rchampeimont/arduino_remote_drawing/3D_model/back.jpg

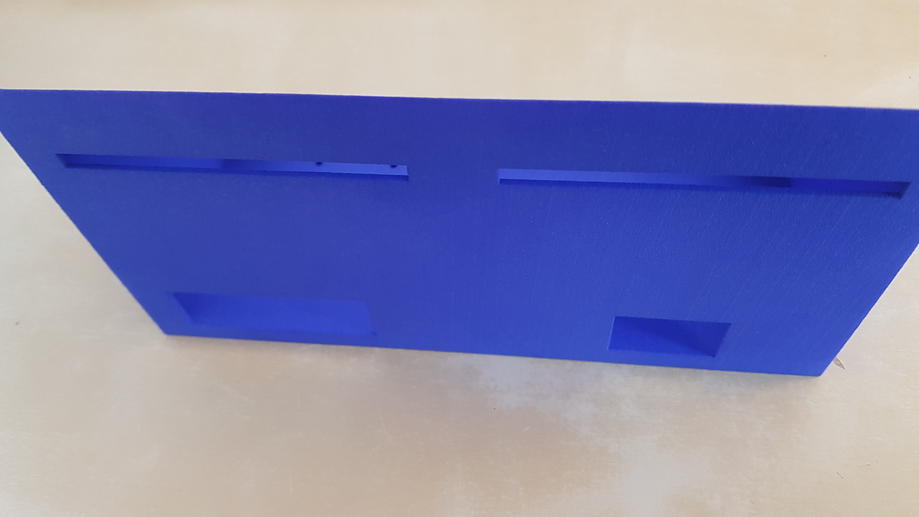
3D_model/back.jpg
