rchampeimont/arduino_remote_drawing/3D_model/bottom.jpg

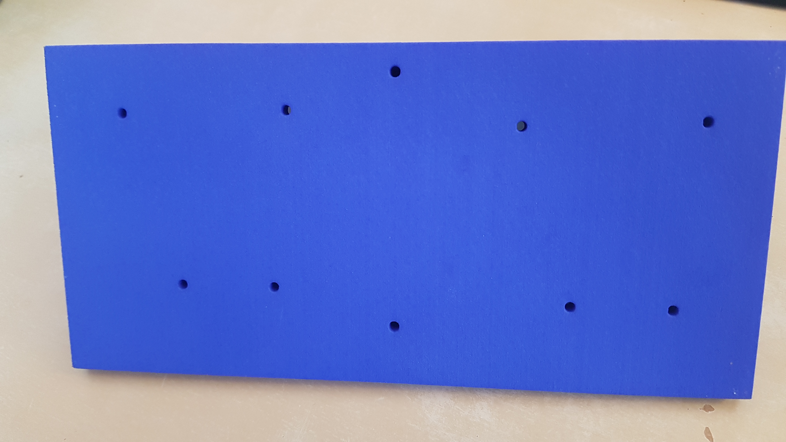
3D_model/bottom.jpg
