rchampeimont/arduino_remote_drawing/3D_model/front.jpg

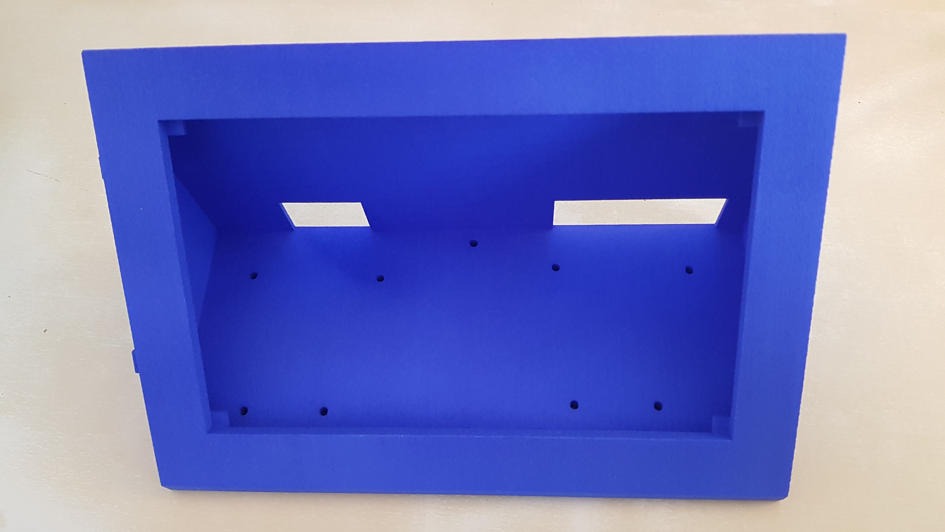
3D_model/front.jpg
