rchampeimont/arduino_remote_drawing/3D_model/left.jpg

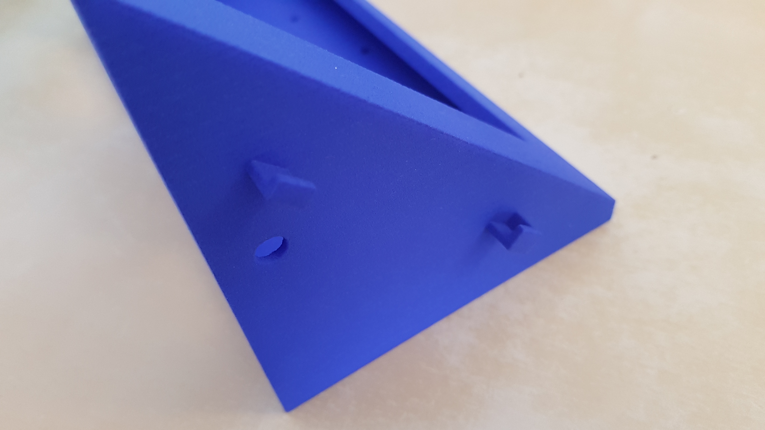
3D_model/left.jpg
