rchampeimont/arduino_remote_drawing/3D_model/right.jpg

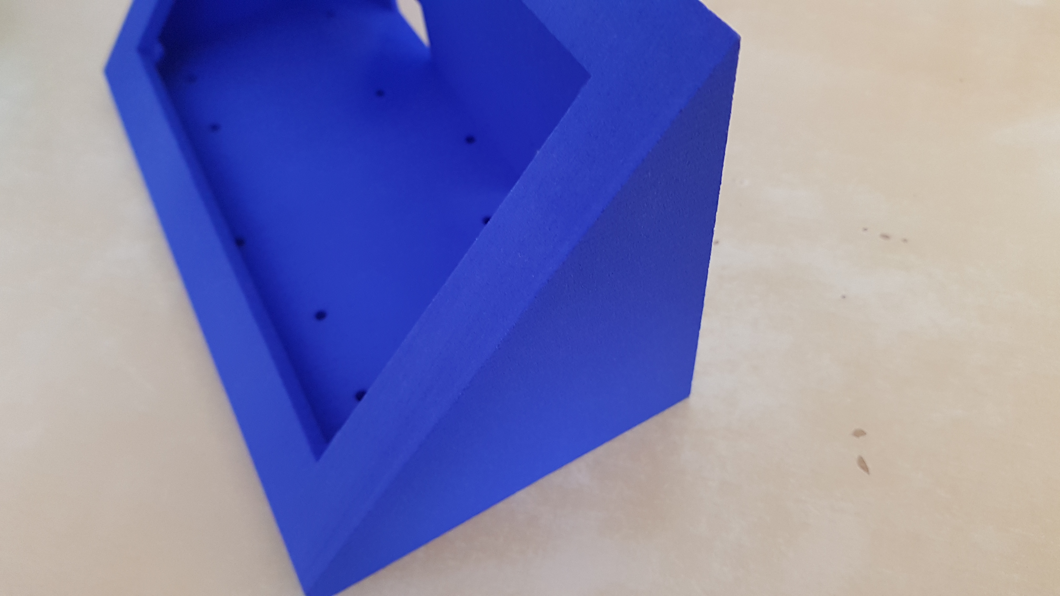
3D_model/right.jpg
