rchampeimont/arduino_remote_drawing/images/inside.jpg

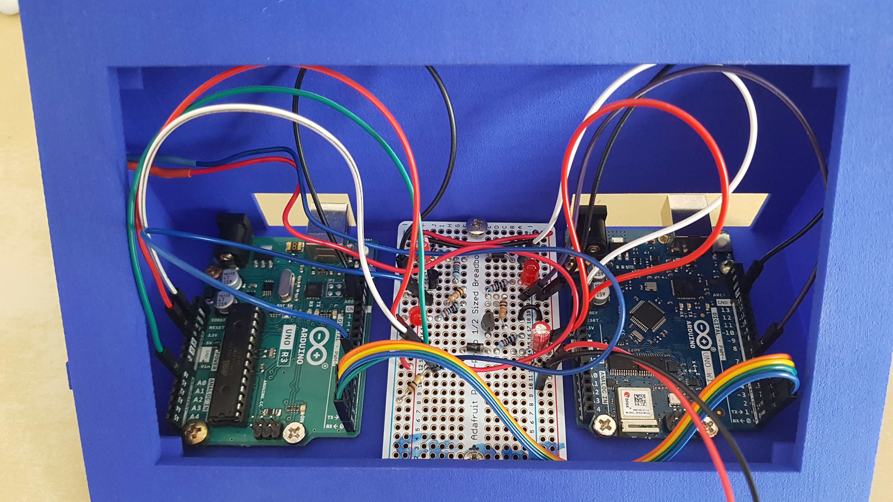
images/inside.jpg
