rchampeimont/arduino_remote_drawing/benchmarks/LINE_MIN_LENGTH/sine/7.jpg

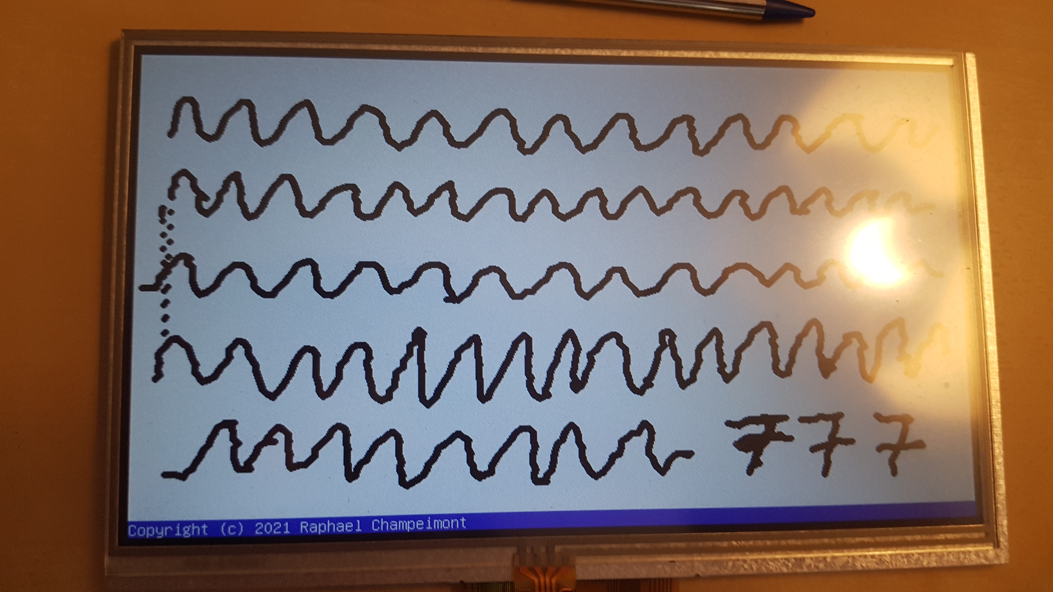
benchmarks/LINE_MIN_LENGTH/sine/7.jpg
