rchampeimont/arduino_remote_drawing/benchmarks/LINE_MIN_LENGTH/snake/10.jpg

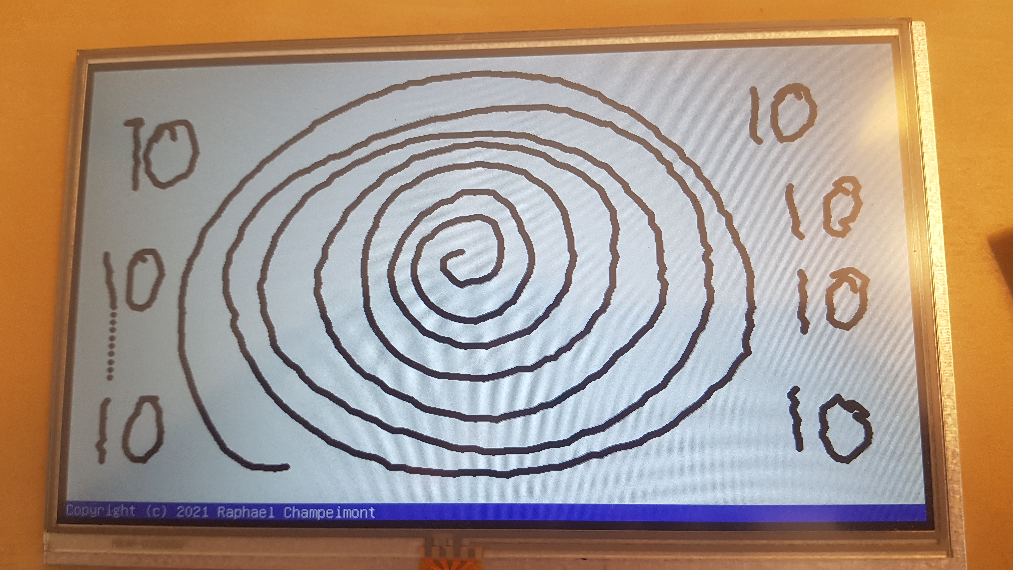
benchmarks/LINE_MIN_LENGTH/snake/10.jpg
