rchampeimont/arduino_remote_drawing/benchmarks/LINE_MIN_LENGTH/snake/15.jpg

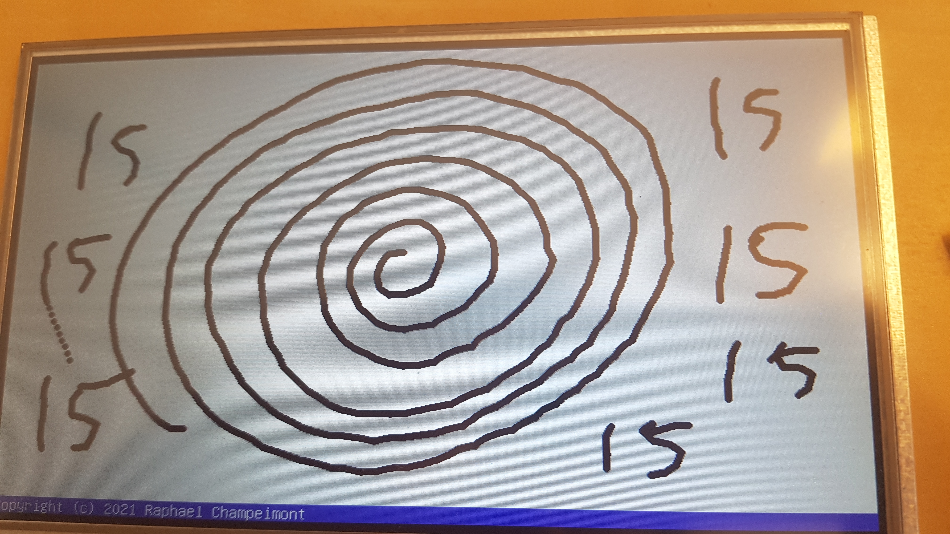
benchmarks/LINE_MIN_LENGTH/snake/15.jpg
