rchampeimont/arduino_remote_drawing/remote_drawing_wifi/system.h

#ifndef SYSTEM_H
#define SYSTEM_H

// Version of Wifi Arduino code
#define VERSION "2.0"

// Pin tied to the other ("UX") Arduino reset circuit
#define PIN_TO_OTHER_ARDUINO_RESET_CIRCUIT 7

// This pin must be pulled LOW on one of the two Wifi Arduinos
#define CLIENT_ID_PIN 5

// Where to detect interrupts coming from the UX Arduino
#define WIFI_ARDUINO_INTERRUPT_PIN 2

// To tell UX Arduino that we are ready to receive drawing data
#define READY_TO_DRAW_PIN 3

// High when we are in an ISR
#define DEBUG_ISR_TIME_PIN 11

// High if fatal error occurs
#define DEBUG_CRASH_PIN 12

// To distiguish this Wifi Arduino from the other Wifi Arduino
extern byte myClientId;

// Reset the other Arduino ("UX" Arduino), which will then reset us (cf. its setup() code)
void resetOther();

// Report that an "alive" signal was received from the other serial-connected Arduino
// Can be called from ISR.
void aliveReceived();

// Check the UX Arduino is alive. To call every 1 second.
void checkAlive();

// Report a fatal error and stop the system
void fatalError(const char *format, ...);

extern volatile byte noResponseFromUxArduinoSeconds;

#endif
